juanmcasillas/Fanashifter/images/csl/csl_02.jpg

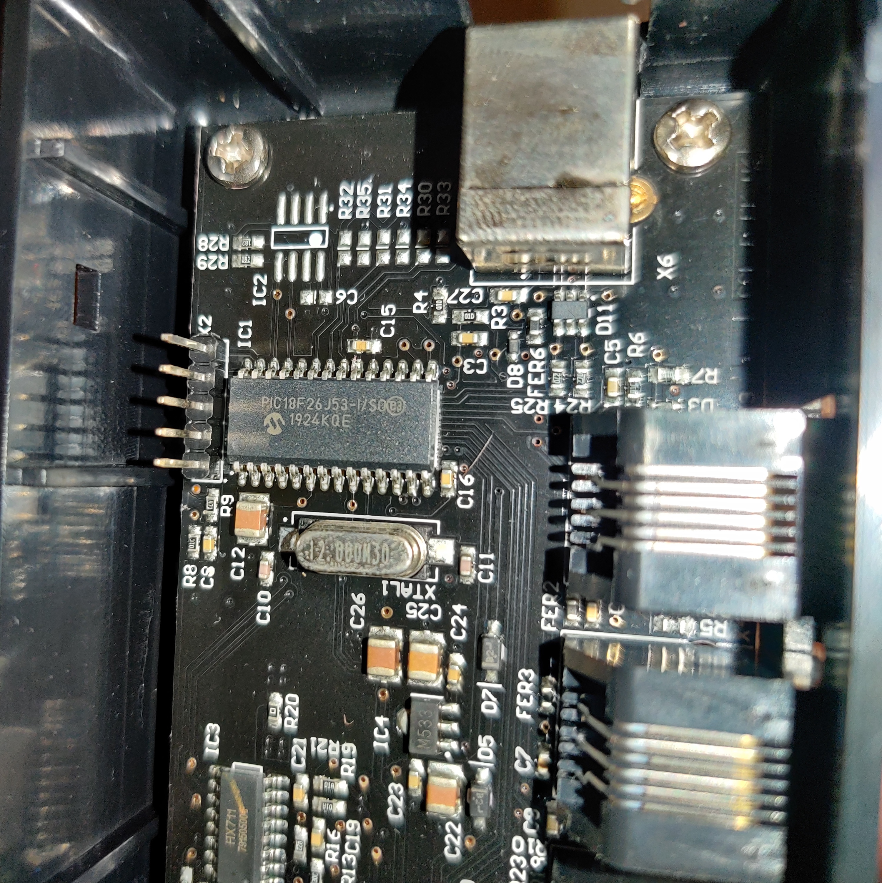
images/csl/csl_02.jpg
