juanmcasillas/Fanashifter/images/csl/csl_04.jpg

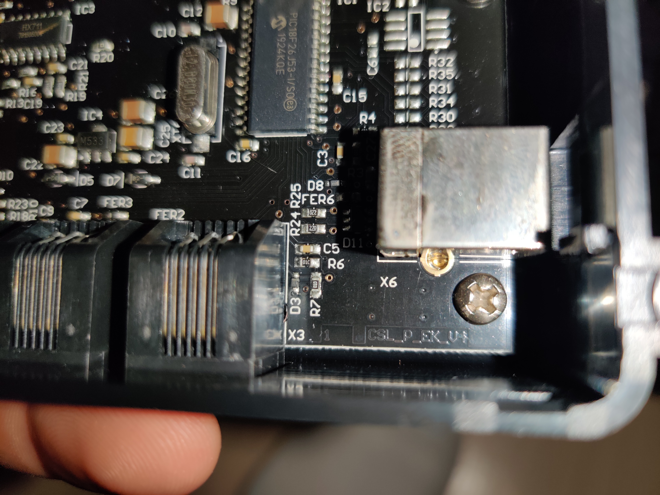
images/csl/csl_04.jpg
