juanmcasillas/Fanashifter/images/csl/rj12_csl_01.png

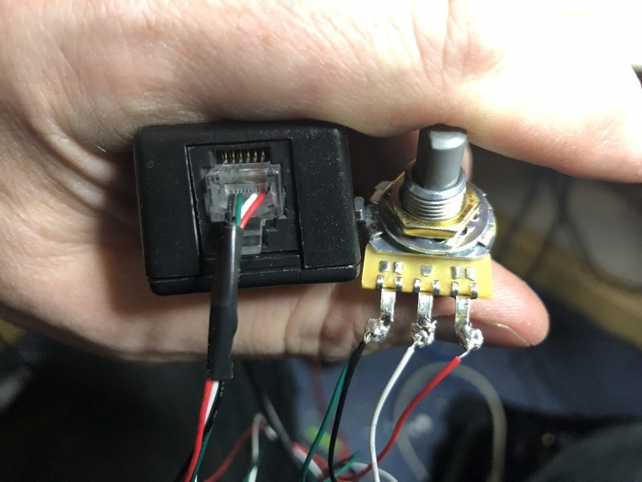
images/csl/rj12_csl_01.png
