juanmcasillas/Fanashifter/images/csl/rj12_csl_02.png

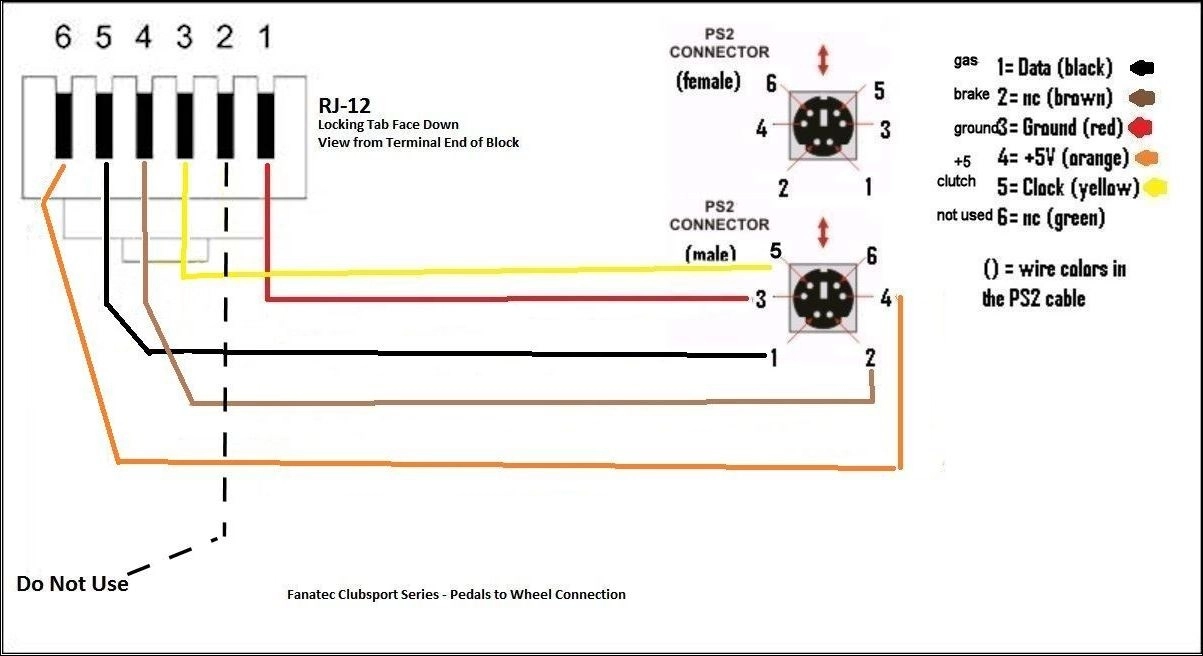
images/csl/rj12_csl_02.png
