juanmcasillas/Fanashifter/images/img/board_up.jpg

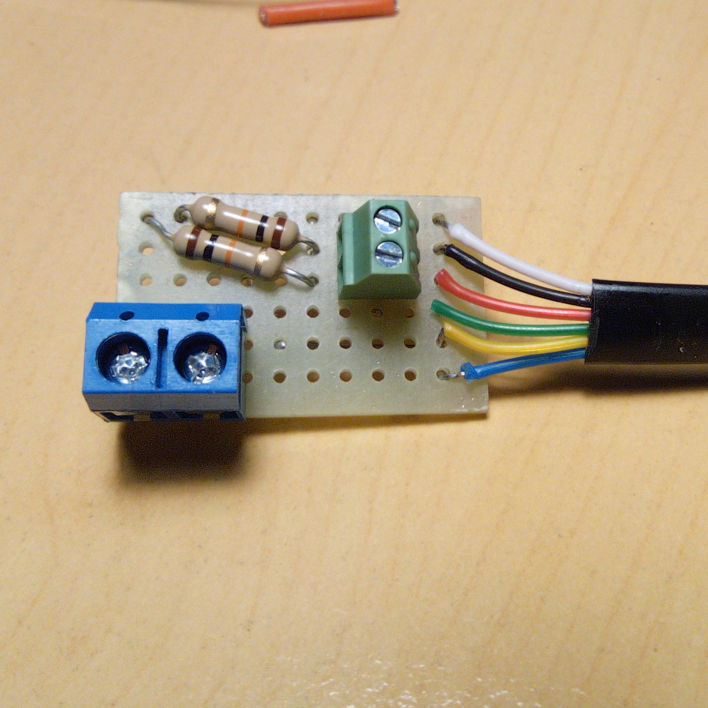
images/img/board_up.jpg
